joaopedrovbs/tapFi/hardware/images/printedDevices.jpg

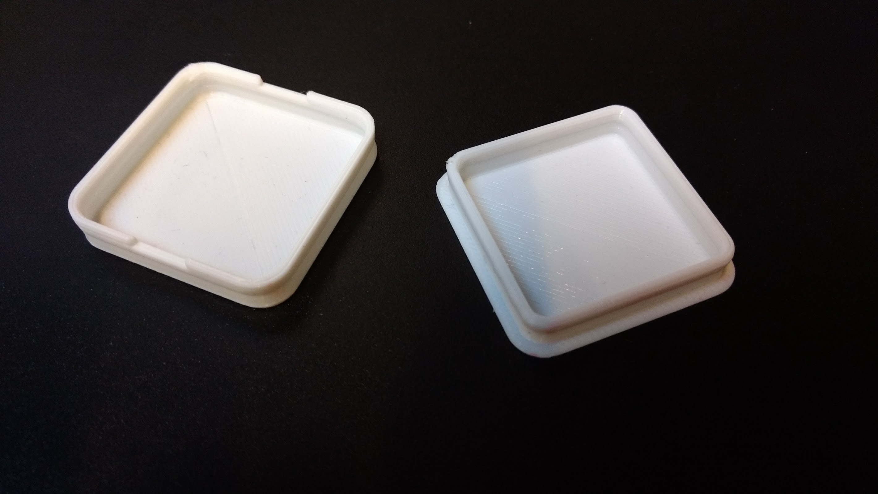
hardware/images/printedDevices.jpg
